3lyktrik/ecoleague/code/arduino/persons.h

// Αντιστοιχία των UID των καρτών RFID με τα ονόματα των κατόχων
// PERSONS_NUMBER είναι ο αντίστοιχος αριθμός των καρτών.

#define PERSONS_NUMBER  12

String cardsUIDs[] = {  "45DE46A781D90",
                        "47EB372891D90",
                        "4F92372891D90",
                        "48D7272891D91",
                        "490CD6A781D90",
                        "4B3E46A781D90",
                        "487472891D94",
                        "11B627C",
                        "515EAC7B",
                        "B3CF7628",
                        "46CE56A781D90",
                        "931A9628"       	};

String names[] = {  "KOMNHNOS", 
                    "THANOS",
                    "ANASTASIA",
                    "LEYTERHS",
                    "APOSTOLOS",
                    "AGGELOS",
                    "GIORGOS",
                    "BASILHS",
                    "XRHSTOS",
                    "SERAFEIM",
                    "NIKH",
                    "ODYSSEAS"      };                  
