3lyktrik/ecoleague/code/arduino/secrets.h

// Use this file to store all of the private credentials 
// and connection details

// Αντικαταστείστε τα XXXXXXX με τους πραγματικούς κωδικούς
// από το λογαριασμό σας στο ThingSpeak
#define SECRET_CH_ID XXXXXXX   			          // my channel number
#define SECRET_WRITE_APIKEY "XXXXXXXXXXXXXXXX"    // my channel write API Key
#define SECRET_READ_APIKEY "XXXXXXXXXXXXXXXX"     // my channel read API Key

// Επίσης τα παρακάτω για το WiFi
#define SECRET_SSID "XXXXXXXXXX"		// WiFi network name
#define SECRET_PASS "XXXXXXXXXX"	    // WiFi password
